pakkid/HexadecipadV2/PCB/screenshots-jlcpcb/100x100.png

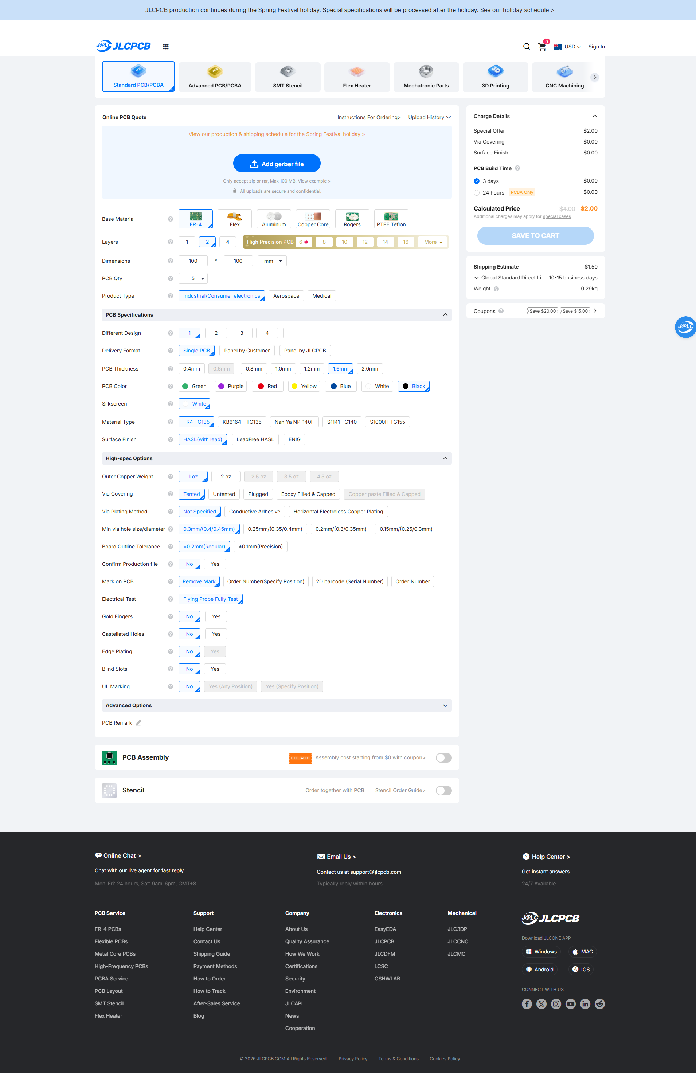
PCB/screenshots-jlcpcb/100x100.png
